StevenMacias/velociruabtor_v2/documentation/System_Design/Fritzing/pictures/04_05_19/photo_2019-05-04_01-13-15.jpg

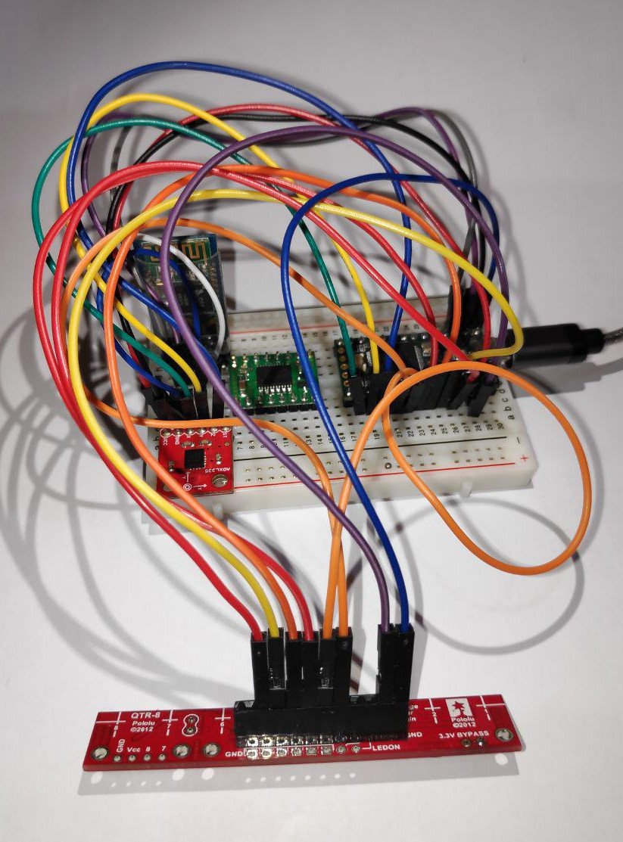
documentation/System_Design/Fritzing/pictures/04_05_19/photo_2019-05-04_01-13-15.jpg
