StevenMacias/velociruabtor_v2/documentation/System_Design/Hardware/Accelerometer-ADXL335/ADXL335-pinout.jpg

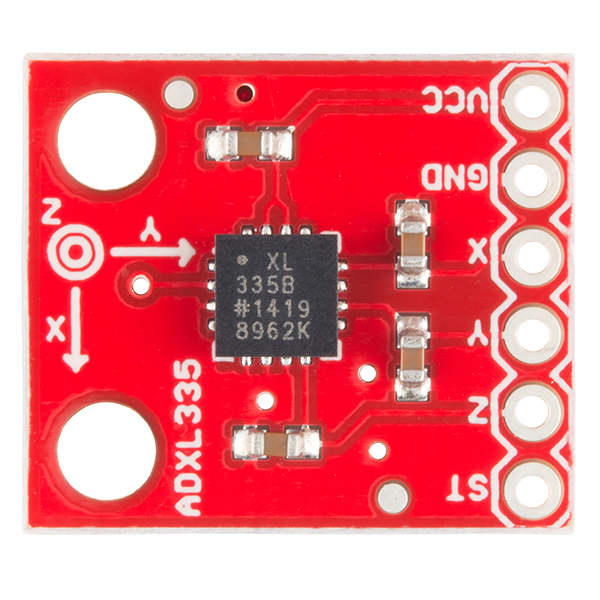
documentation/System_Design/Hardware/Accelerometer-ADXL335/ADXL335-pinout.jpg
