StevenMacias/velociruabtor_v2/documentation/System_Design/Hardware/Teensy_3_2/teensy_3_2-back_pinout.png

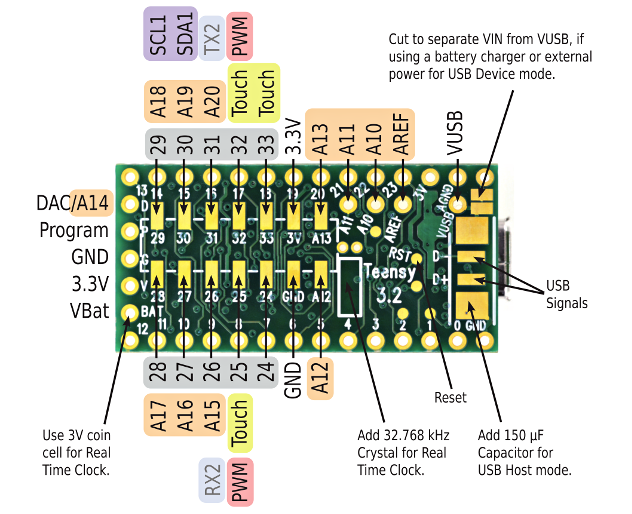
documentation/System_Design/Hardware/Teensy_3_2/teensy_3_2-back_pinout.png
