StevenMacias/velociruabtor_v2/documentation/System_Design/Hardware/Teensy_3_2/teensy_3_2-front_pinout.png

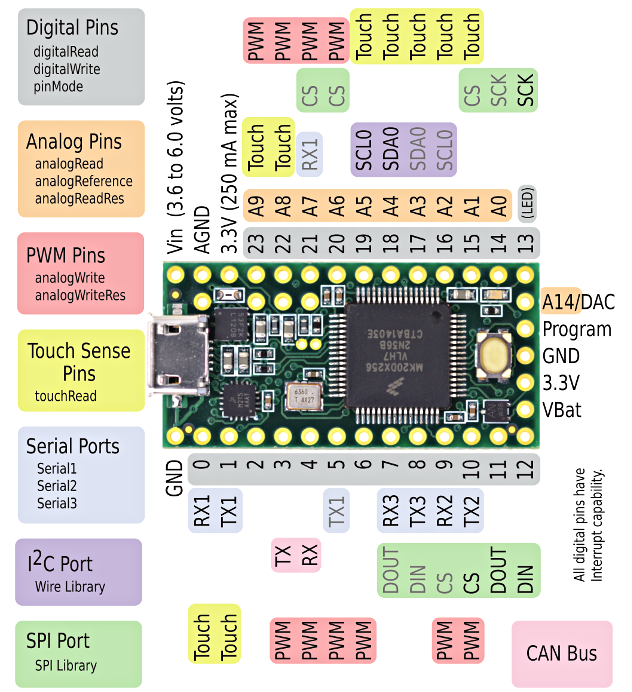
documentation/System_Design/Hardware/Teensy_3_2/teensy_3_2-front_pinout.png
