StevenMacias/velociruabtor_v2/documentation/wiki/images/photo_2019-09-26_14-32-05.jpg

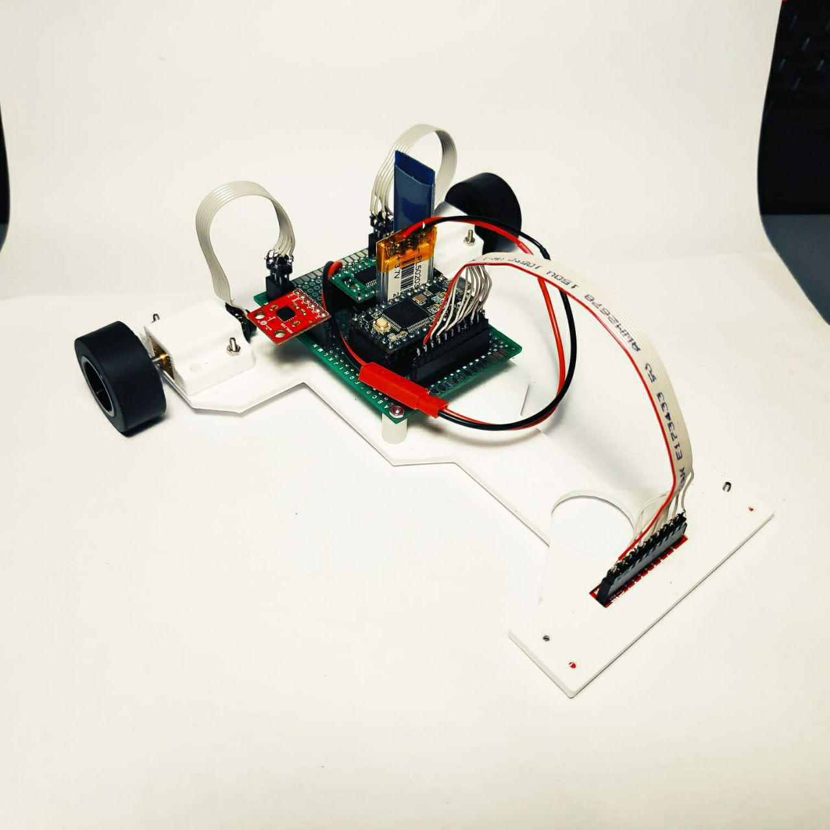
documentation/wiki/images/photo_2019-09-26_14-32-05.jpg
