StevenMacias/velociruabtor_v2/documentation/wiki/images/tht-back-v1_0.jpg

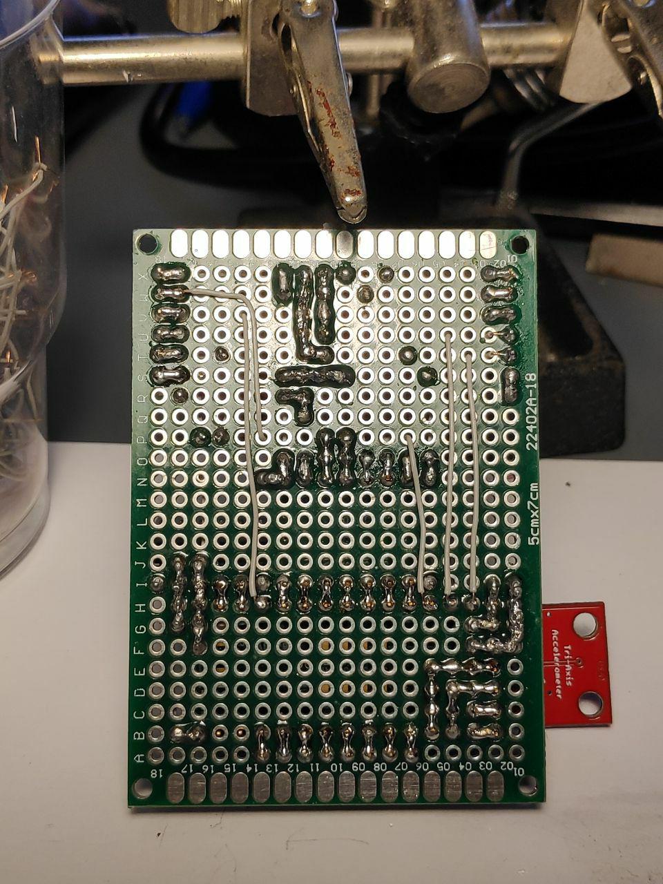
documentation/wiki/images/tht-back-v1_0.jpg
