StevenMacias/velociruabtor_v2/documentation/wiki/images/tht-front-v1_0.jpg

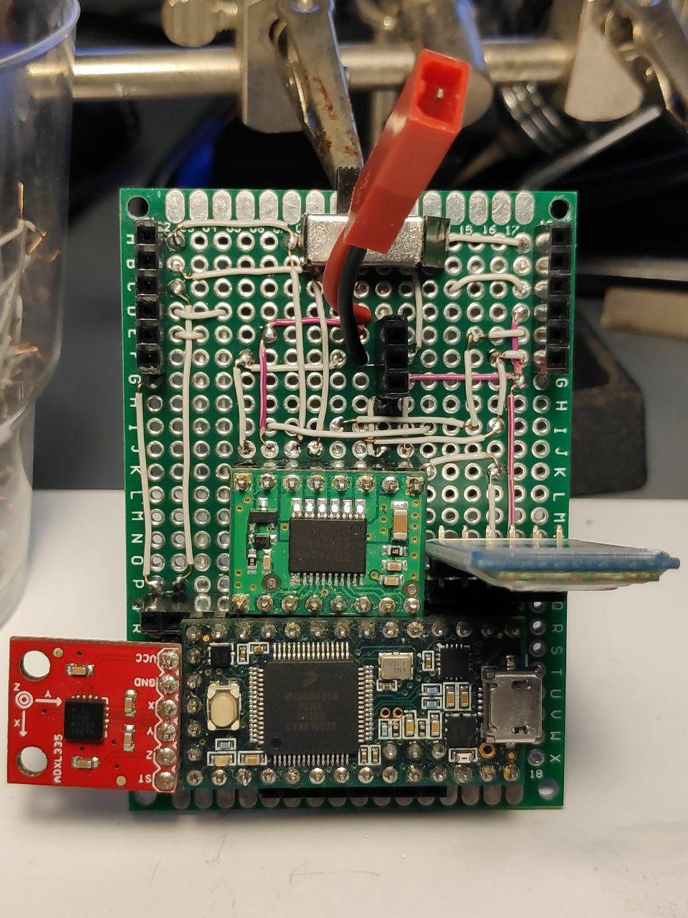
documentation/wiki/images/tht-front-v1_0.jpg
