StevenMacias/velociruabtor_v2/documentation/wiki/images/valuesJson.png

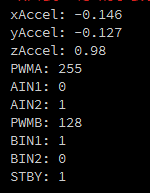
documentation/wiki/images/valuesJson.png
