StevenMacias/velociruabtor_v2/documentation/wiki/images/velociruabtor2-v0_1.jpg

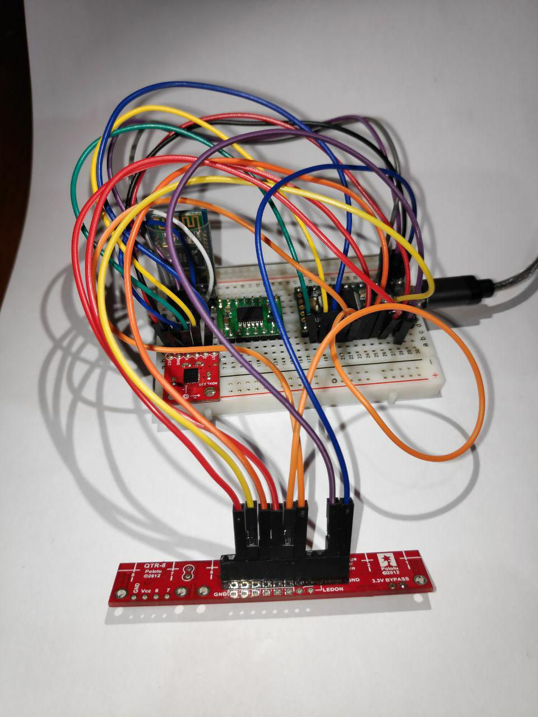
documentation/wiki/images/velociruabtor2-v0_1.jpg
